twop/forager-travel-case/images/finished-case-opened.jpeg

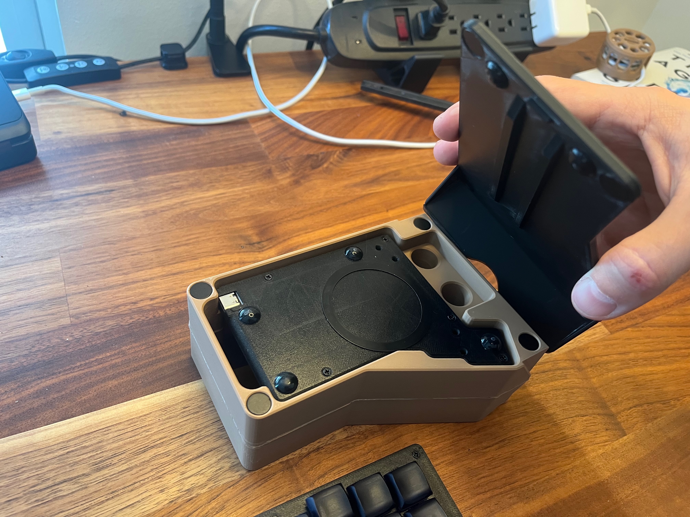
images/finished-case-opened.jpeg
